RyanAbsher/The-Force/Photos/2.jpg

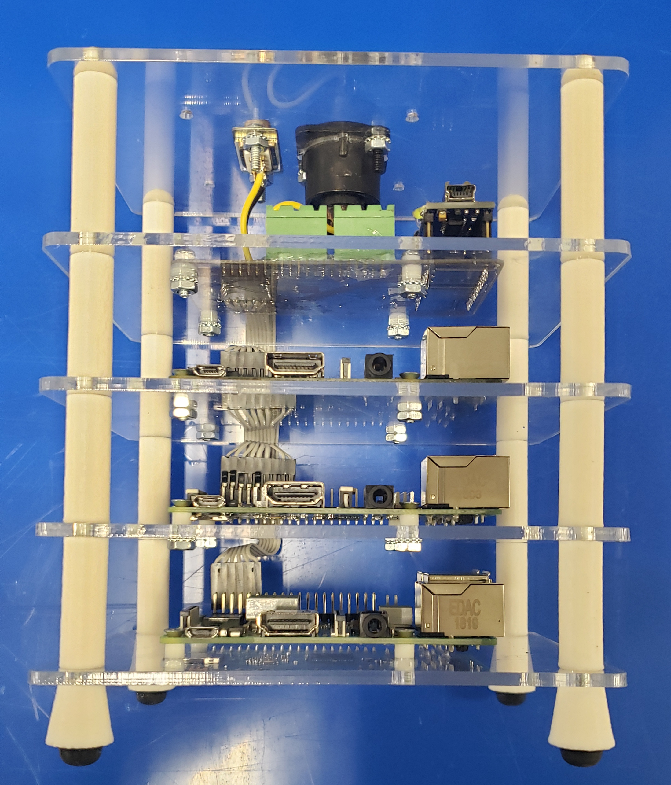
Photos/2.jpg
