RyanAbsher/The-Force/Photos/3.jpg

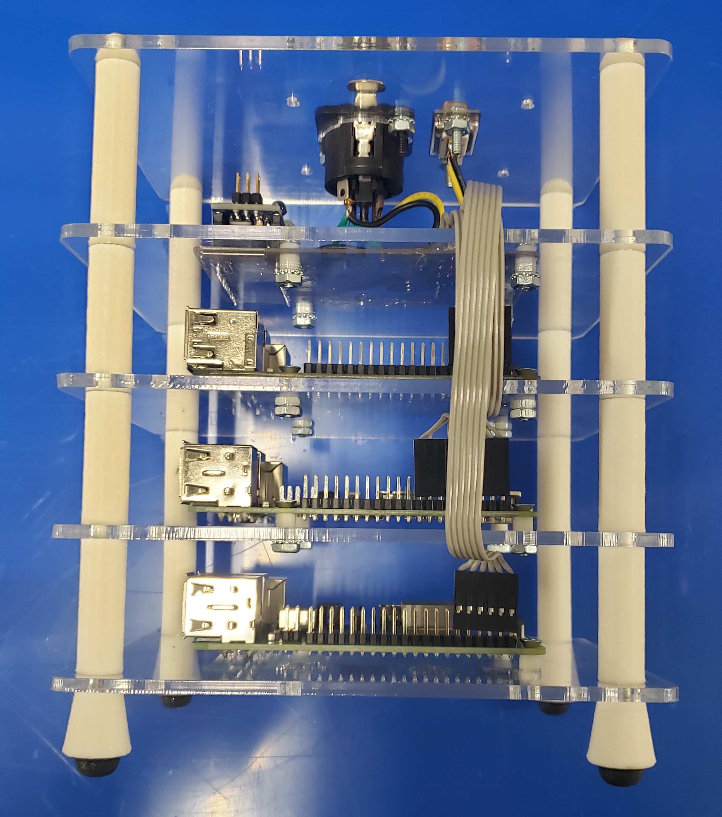
Photos/3.jpg
