RyanAbsher/The-Force/Arduino/RS-232_DMX/showDef.h

#define NUM_DEF 296
const byte fixtureNumber[297]= {20, 21, 20, 21, 20, 21, 20, 21, 20, 21, 20, 21, 20, 21, 20, 21, 20, 21, 20, 21, 20, 21, 20, 21, 20, 21, 20, 21, 20, 21, 20, 21, 20, 21, 20, 21, 20, 21, 20, 21, 20, 21, 20, 21, 20, 21, 20, 21, 20, 21, 20, 21, 20, 21, 20, 21, 20, 21, 20, 21, 20, 21, 20, 21, 20, 21, 20, 21, 20, 21, 20, 21, 20, 21, 20, 21, 20, 21, 20, 21, 20, 21, 20, 21, 20, 21, 20, 21, 20, 21, 20, 21, 20, 21, 20, 21, 20, 21, 20, 21, 20, 21, 20, 21, 20, 21, 20, 21, 20, 21, 20, 21, 20, 21, 20, 21, 20, 21, 20, 21, 20, 21, 20, 21, 20, 21, 20, 21, 20, 21, 20, 21, 20, 21, 20, 21, 20, 21, 20, 21, 20, 21, 20, 21, 20, 21, 20, 21, 20, 21, 20, 21, 20, 21, 20, 21, 20, 21, 20, 21, 20, 21, 20, 21, 20, 21, 20, 21, 20, 21, 20, 21, 20, 21, 20, 21, 20, 21, 20, 21, 20, 21, 20, 21, 20, 21, 20, 21, 20, 21, 20, 21, 20, 21, 20, 21, 20, 21, 20, 21, 20, 21, 20, 21, 20, 21, 20, 21, 20, 21, 20, 21, 20, 21, 20, 21, 47, 51, 47, 51, 47, 51, 47, 51, 47, 51, 47, 51, 47, 51, 47, 51, 47, 51, 47, 51, 47, 51, 47, 51, 47, 51, 47, 51, 47, 51, 47, 51, 47, 51, 47, 51, 47, 51, 47, 51, 47, 51, 47, 51, 47, 51, 47, 51, 47, 51, 47, 51, 47, 51, 2, 7, 20, 21, 47, 51, 73, 101, 2, 7, 21, 47, 51, 73, 101, 20, 20, 20, 20, 20, 20, 20, 20, 20, 20, 20, 20};
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
